NimmLor/7-Segement-Clock/images/arduino_code.PNG

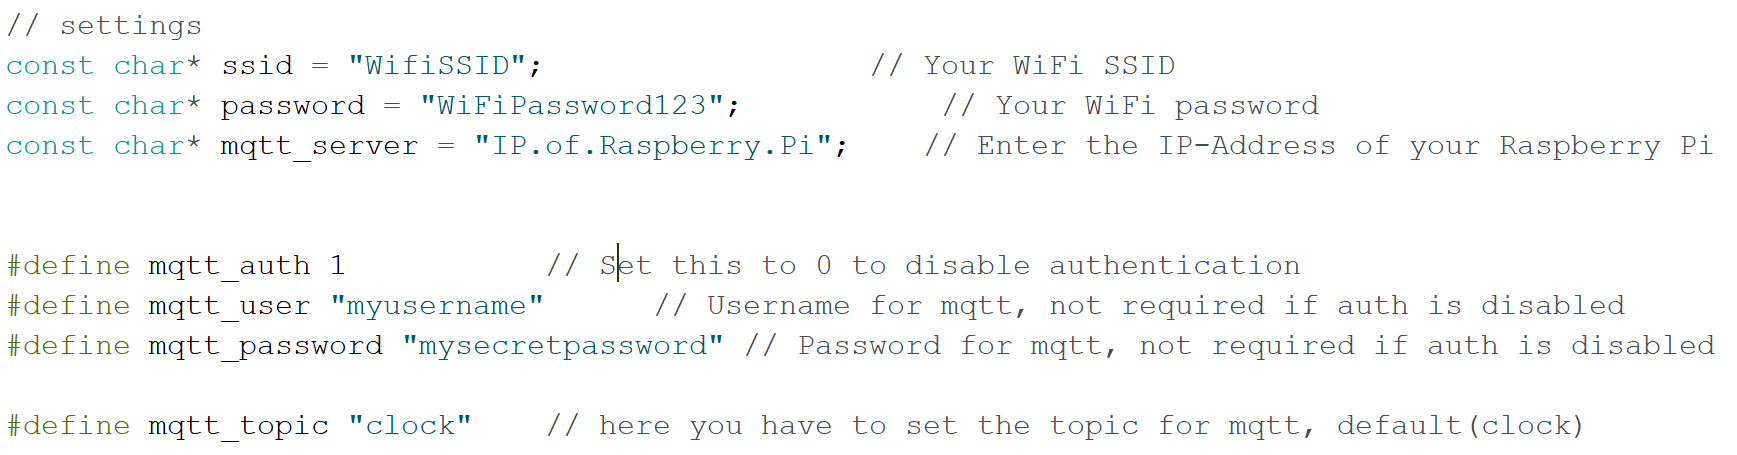
images/arduino_code.PNG
