NimmLor/7-Segement-Clock/images/customize_dashboards2.PNG

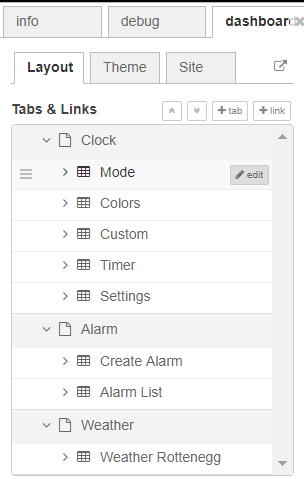
images/customize_dashboards2.PNG
