NimmLor/7-Segement-Clock/images/customize_webinterface.PNG

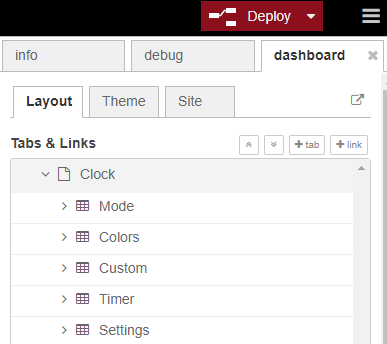
images/customize_webinterface.PNG
