NimmLor/7-Segement-Clock/images/DSC_1147.JPG

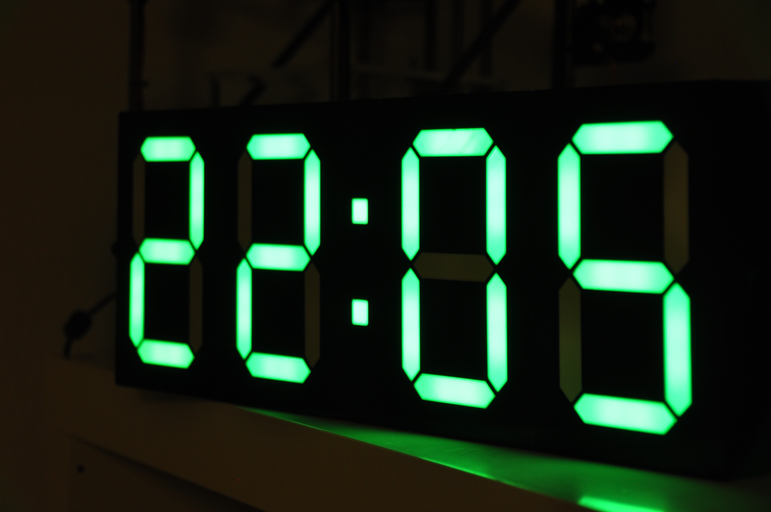
images/DSC_1147.JPG
