NimmLor/7-Segement-Clock/images/DSC_1149.JPG

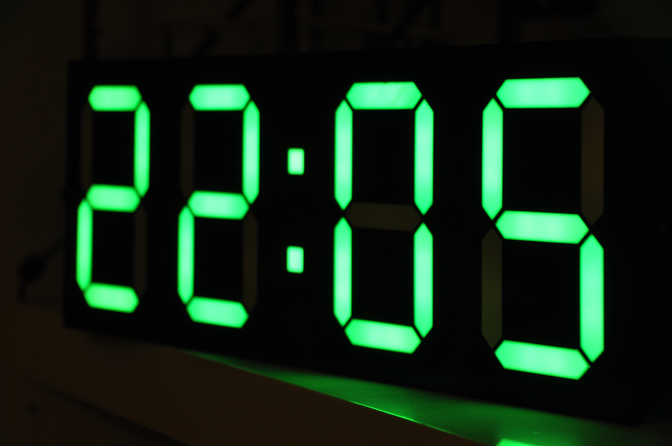
images/DSC_1149.JPG
