NimmLor/7-Segement-Clock/images/DSC_1150.JPG

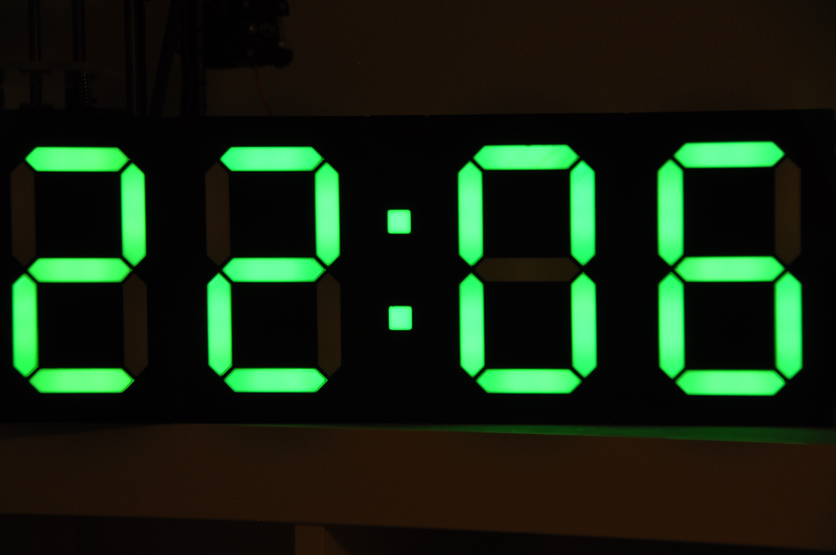
images/DSC_1150.JPG
