NimmLor/7-Segement-Clock/images/DSC_1151.JPG

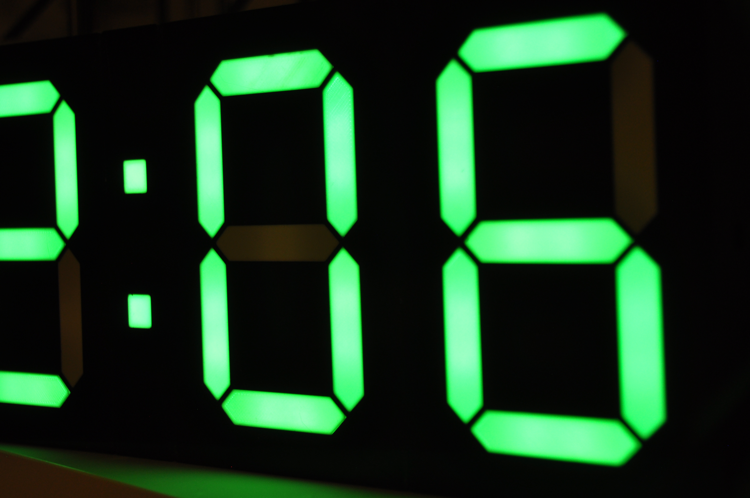
images/DSC_1151.JPG
