NimmLor/7-Segement-Clock/images/DSC_1152.JPG

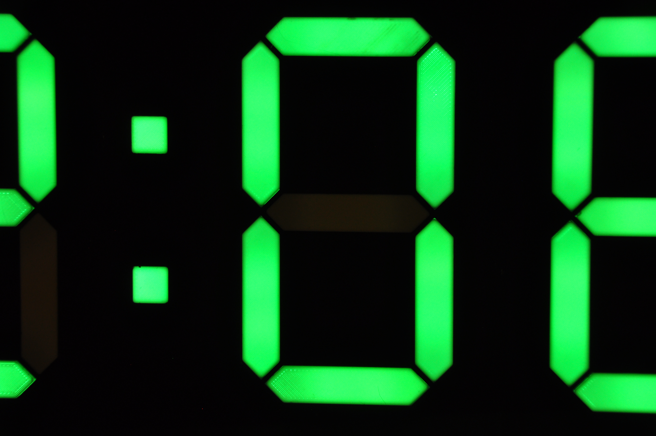
images/DSC_1152.JPG
