NimmLor/7-Segement-Clock/images/DSC_1153.JPG

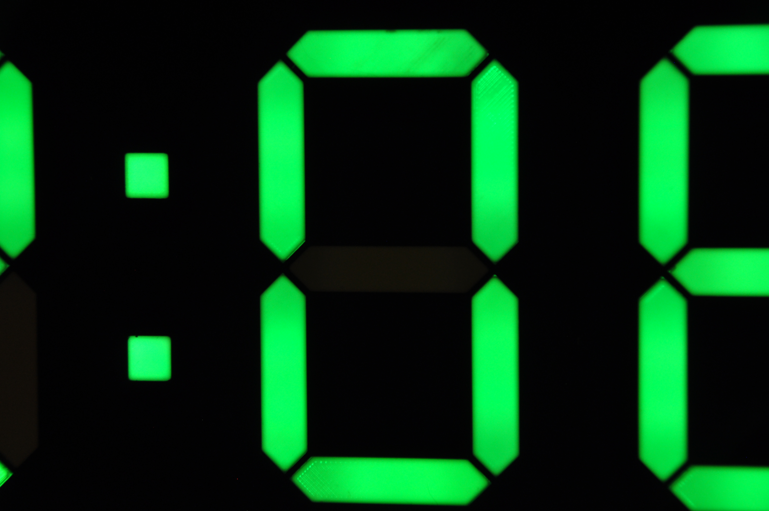
images/DSC_1153.JPG
