NimmLor/7-Segement-Clock/images/DSC_1157.JPG

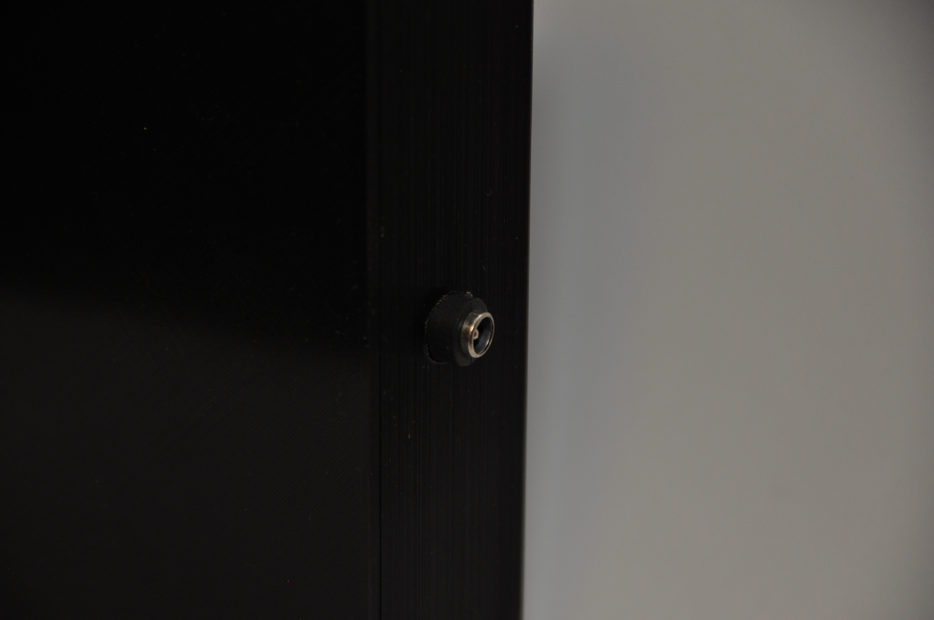
images/DSC_1157.JPG
