NimmLor/7-Segement-Clock/images/DSC_1158.JPG

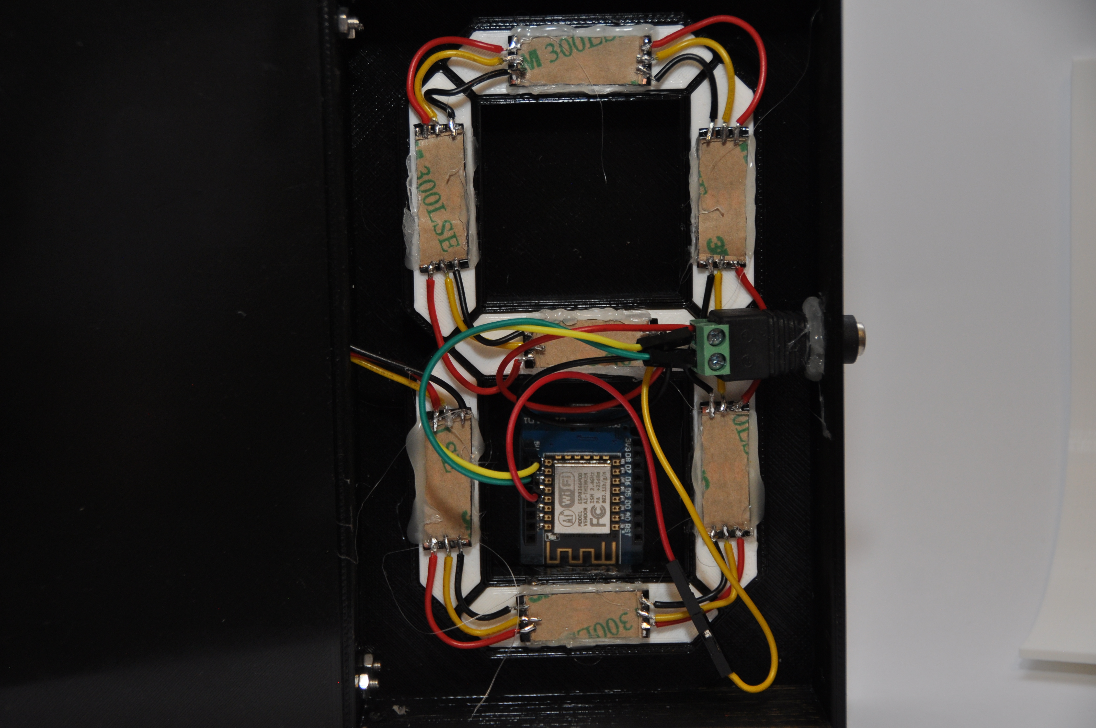
images/DSC_1158.JPG
