NimmLor/7-Segement-Clock/images/DSC_1159.JPG

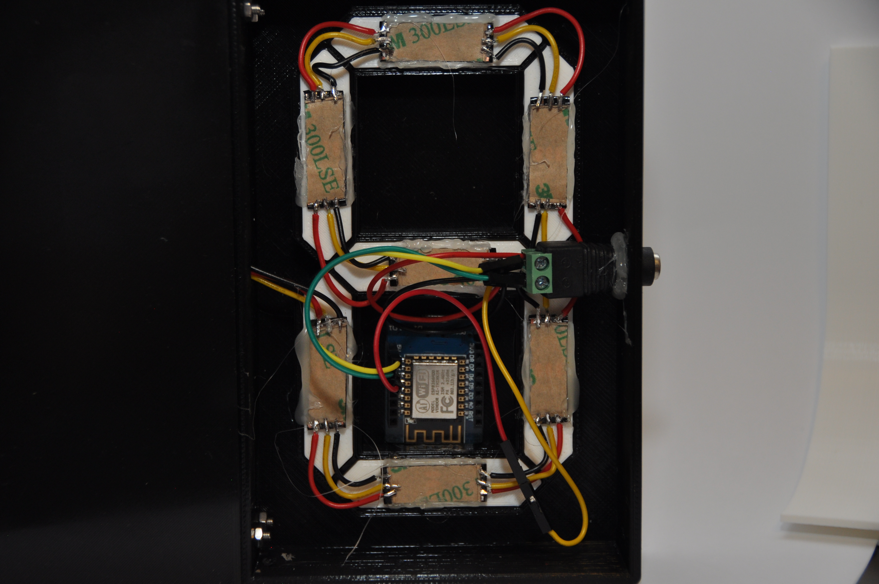
images/DSC_1159.JPG
