NimmLor/7-Segement-Clock/images/DSC_1160.JPG

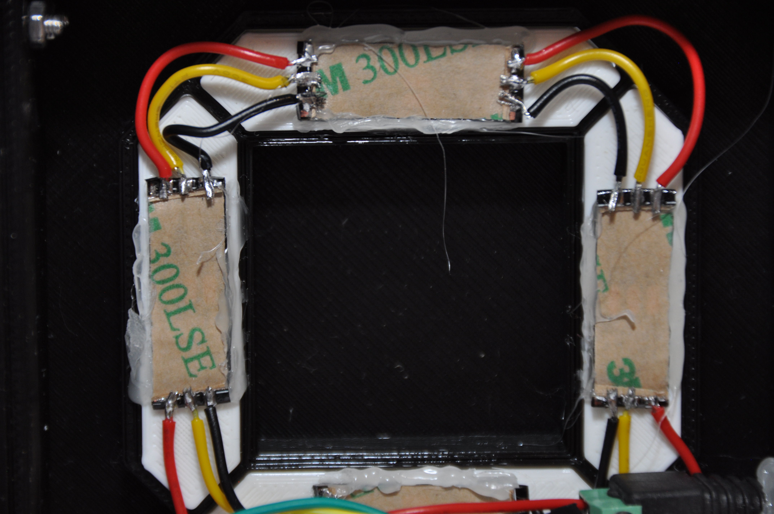
images/DSC_1160.JPG
