NimmLor/7-Segement-Clock/images/DSC_1161.JPG

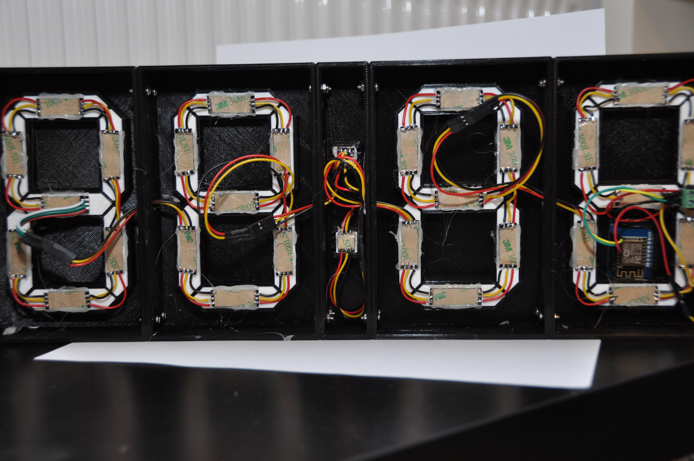
images/DSC_1161.JPG
