NimmLor/7-Segement-Clock/images/DSC_1162.JPG

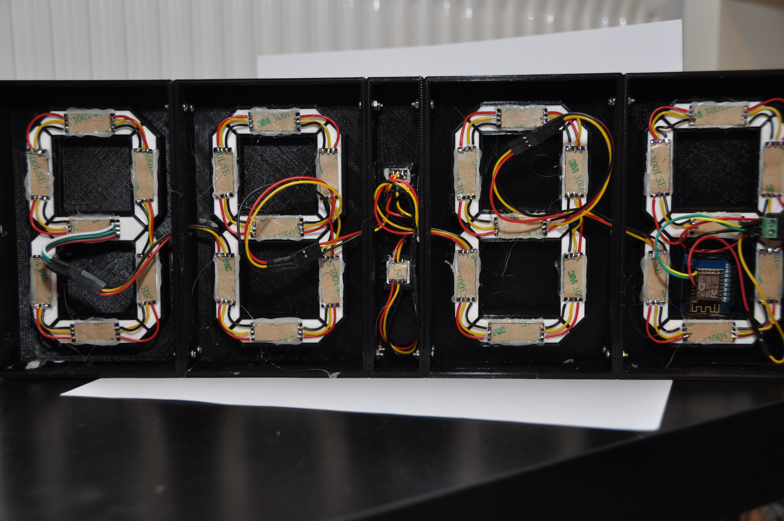
images/DSC_1162.JPG
