NimmLor/7-Segement-Clock/images/DSC_1163.JPG

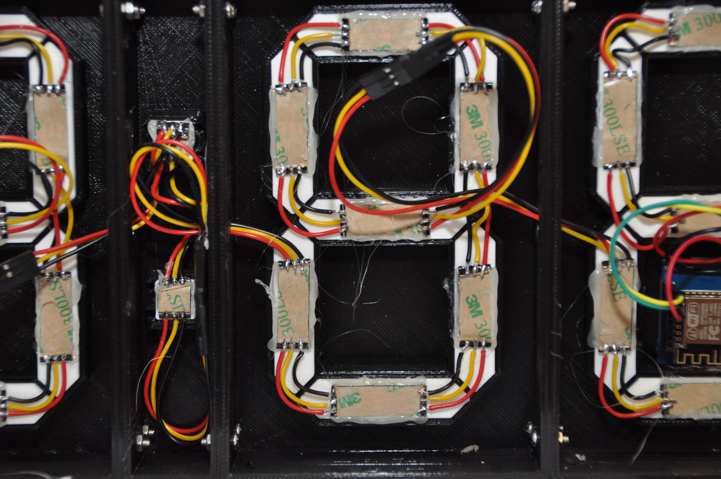
images/DSC_1163.JPG
