NimmLor/7-Segement-Clock/images/DSC_1164.JPG

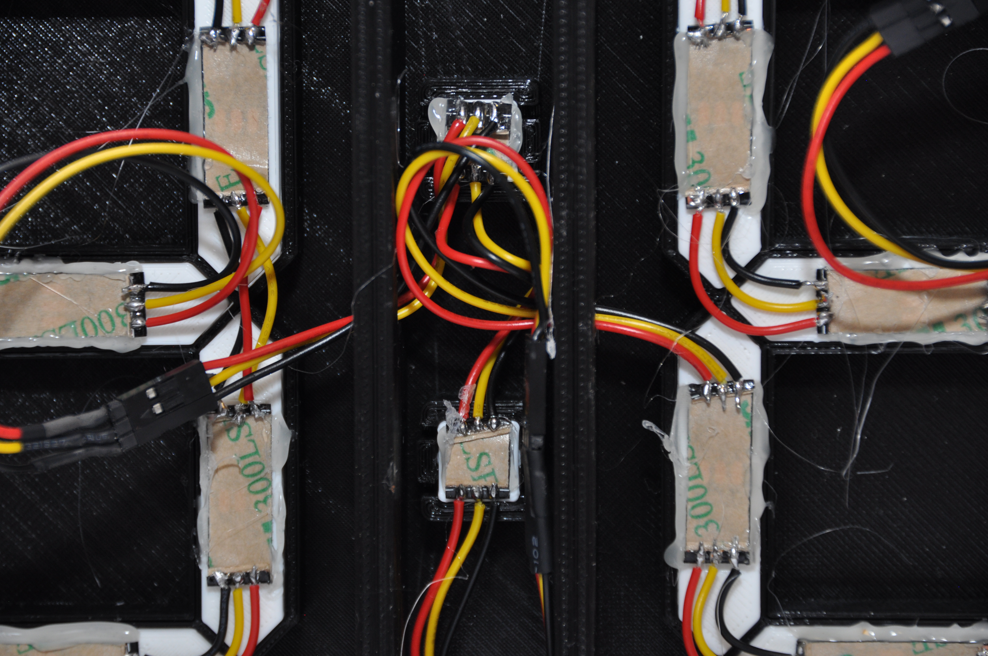
images/DSC_1164.JPG
