NimmLor/7-Segement-Clock/images/DSC_1166.JPG

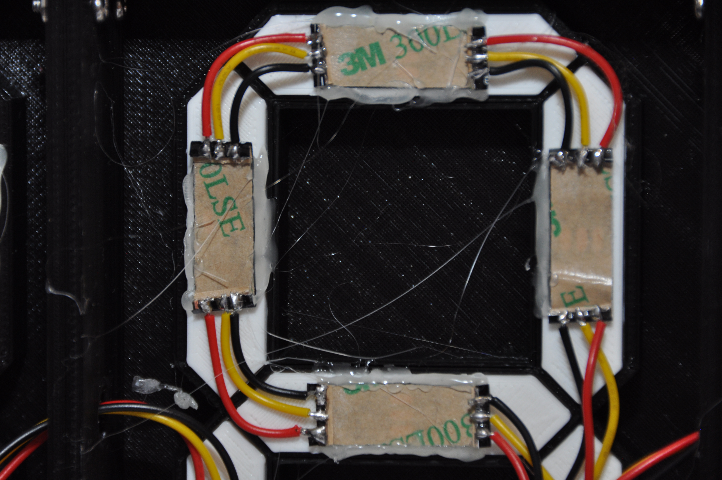
images/DSC_1166.JPG
