NimmLor/7-Segement-Clock/images/DSC_1168.JPG

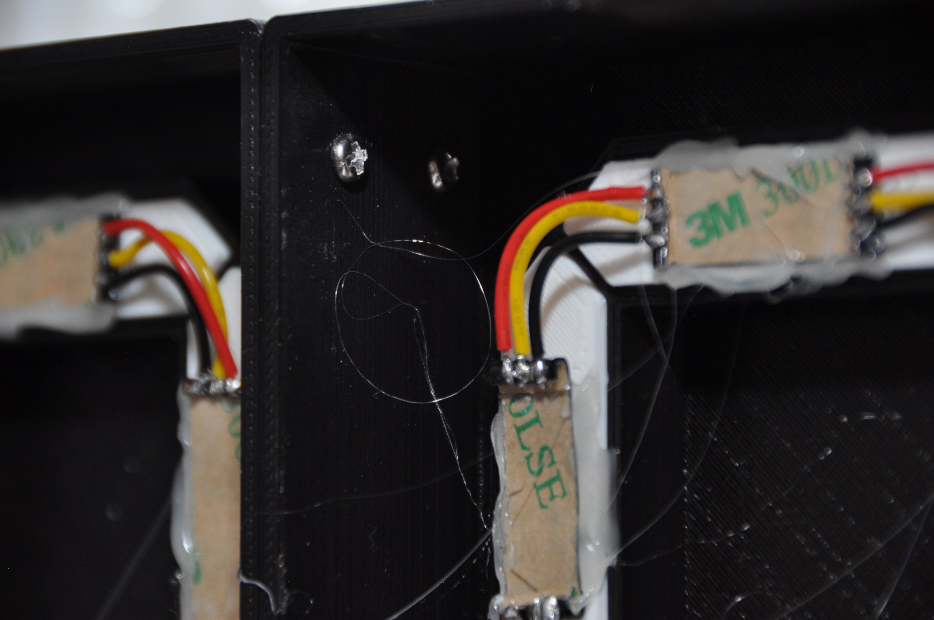
images/DSC_1168.JPG
