NimmLor/7-Segement-Clock/images/DSC_1169.JPG

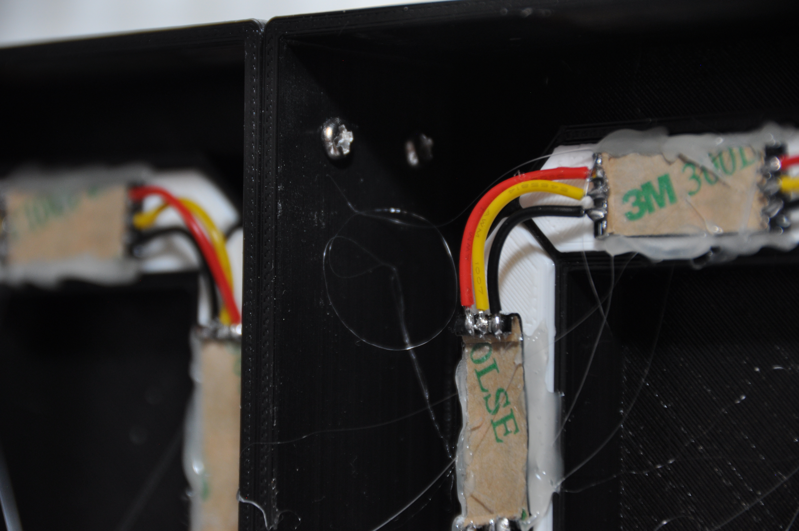
images/DSC_1169.JPG
