NimmLor/7-Segement-Clock/images/DSC_1170.JPG

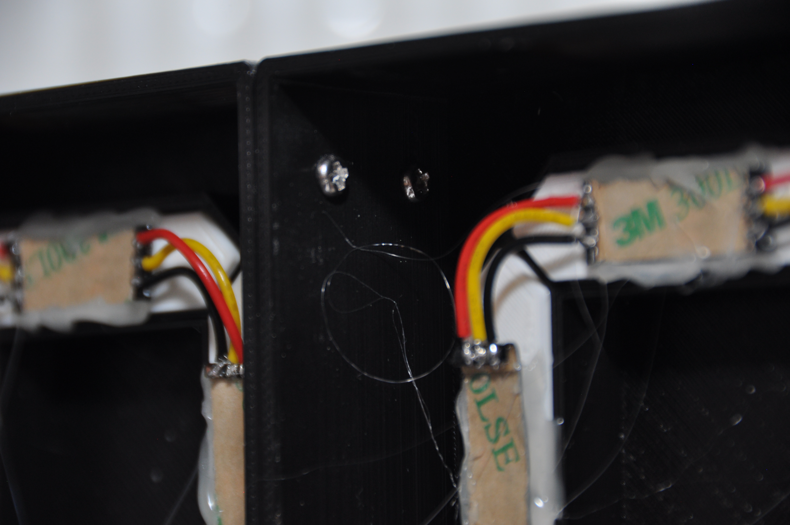
images/DSC_1170.JPG
