NimmLor/7-Segement-Clock/images/DSC_1171.JPG

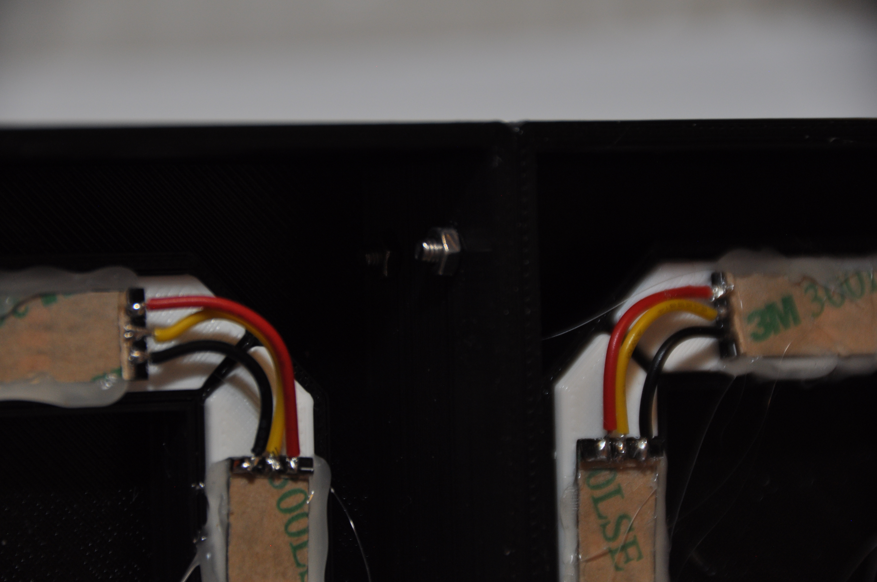
images/DSC_1171.JPG
