NimmLor/7-Segement-Clock/images/DSC_1172.JPG

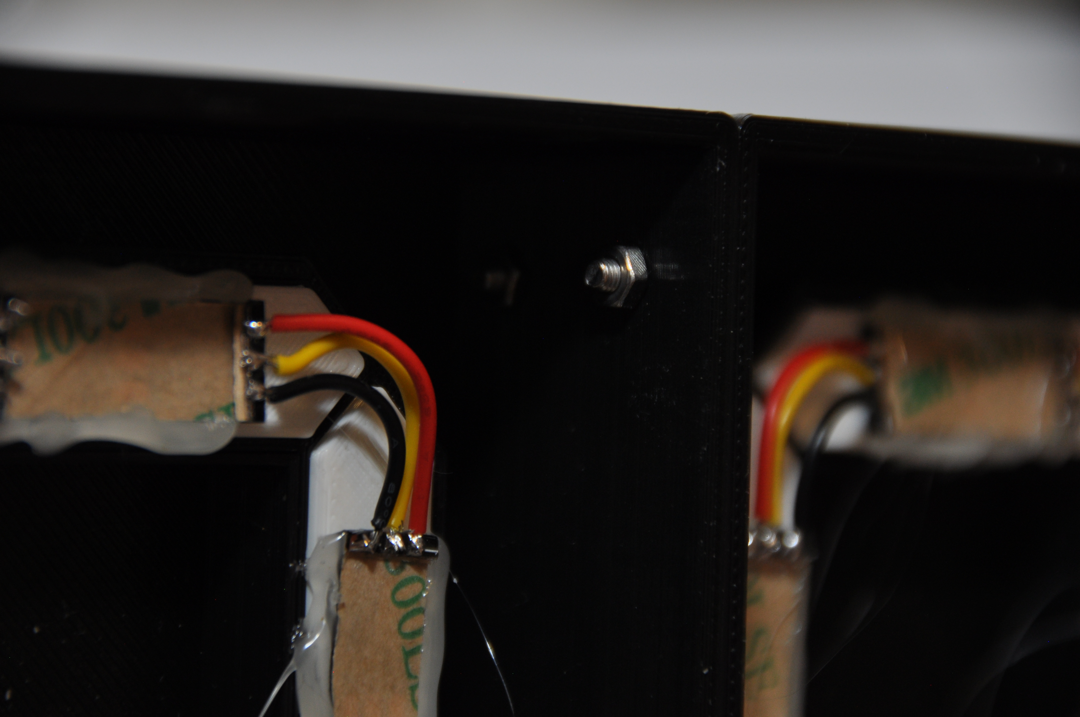
images/DSC_1172.JPG
