NimmLor/7-Segement-Clock/images/DSC_1175.JPG

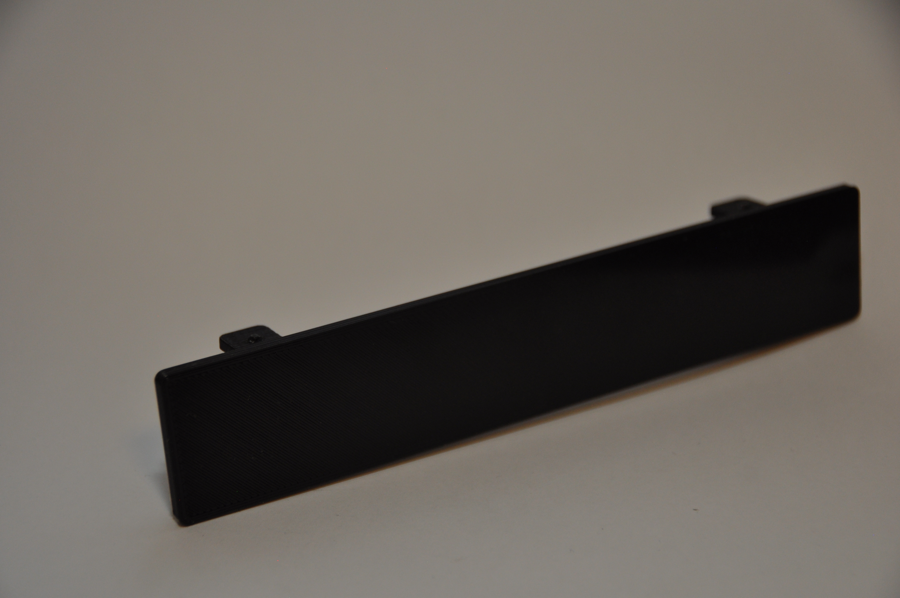
images/DSC_1175.JPG
