NimmLor/7-Segement-Clock/images/DSC_1179.JPG

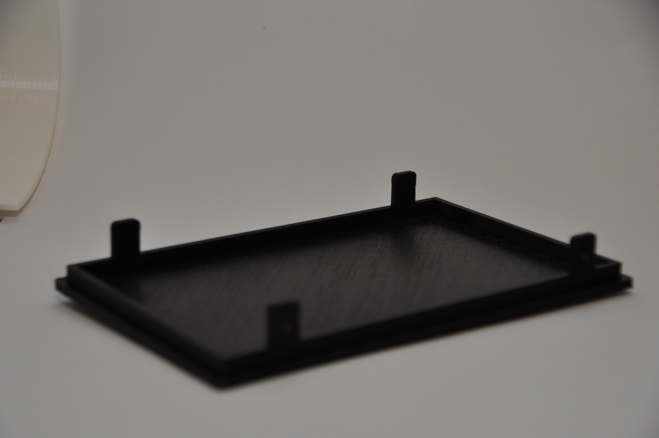
images/DSC_1179.JPG
