NimmLor/7-Segement-Clock/images/DSC_1180.JPG

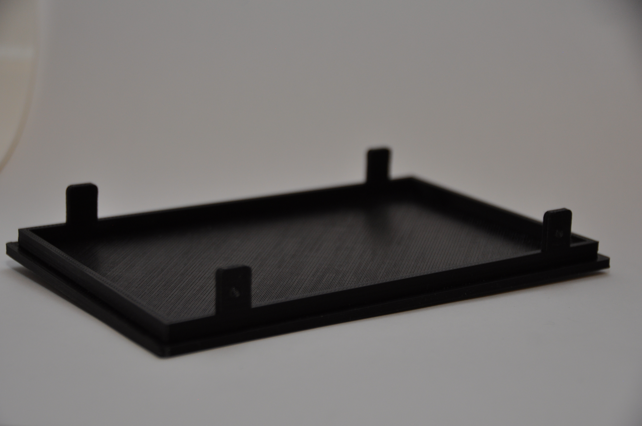
images/DSC_1180.JPG
