NimmLor/7-Segement-Clock/images/DSC_1181.JPG

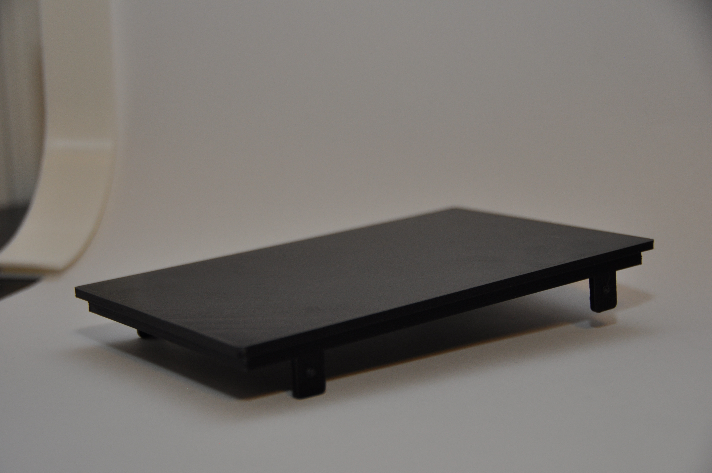
images/DSC_1181.JPG
