NimmLor/7-Segement-Clock/images/DSC_1182.JPG

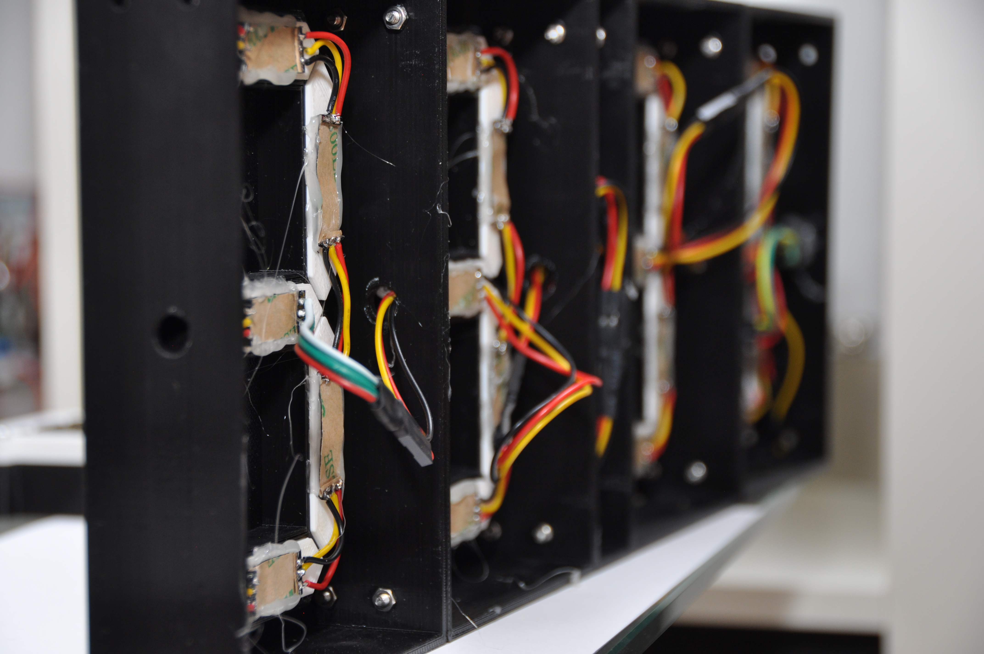
images/DSC_1182.JPG
