NimmLor/7-Segement-Clock/images/DSC_1184.JPG

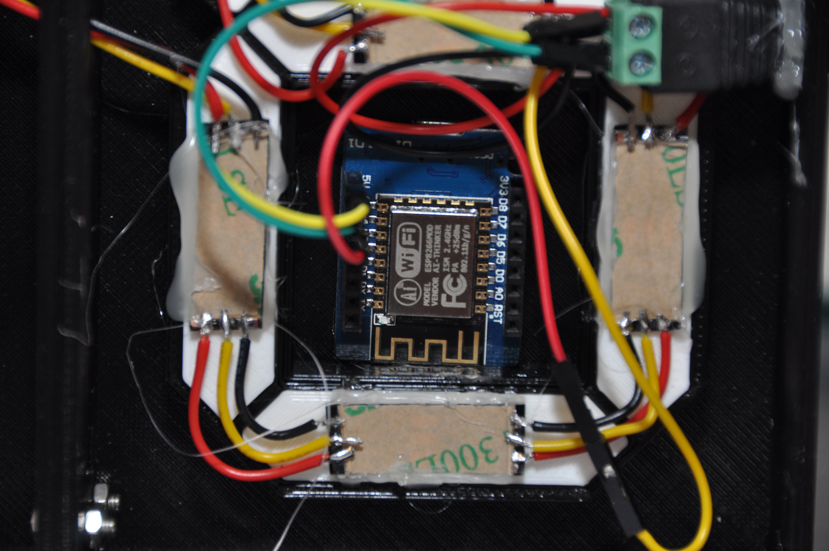
images/DSC_1184.JPG
