NimmLor/7-Segement-Clock/images/DSC_1185.JPG

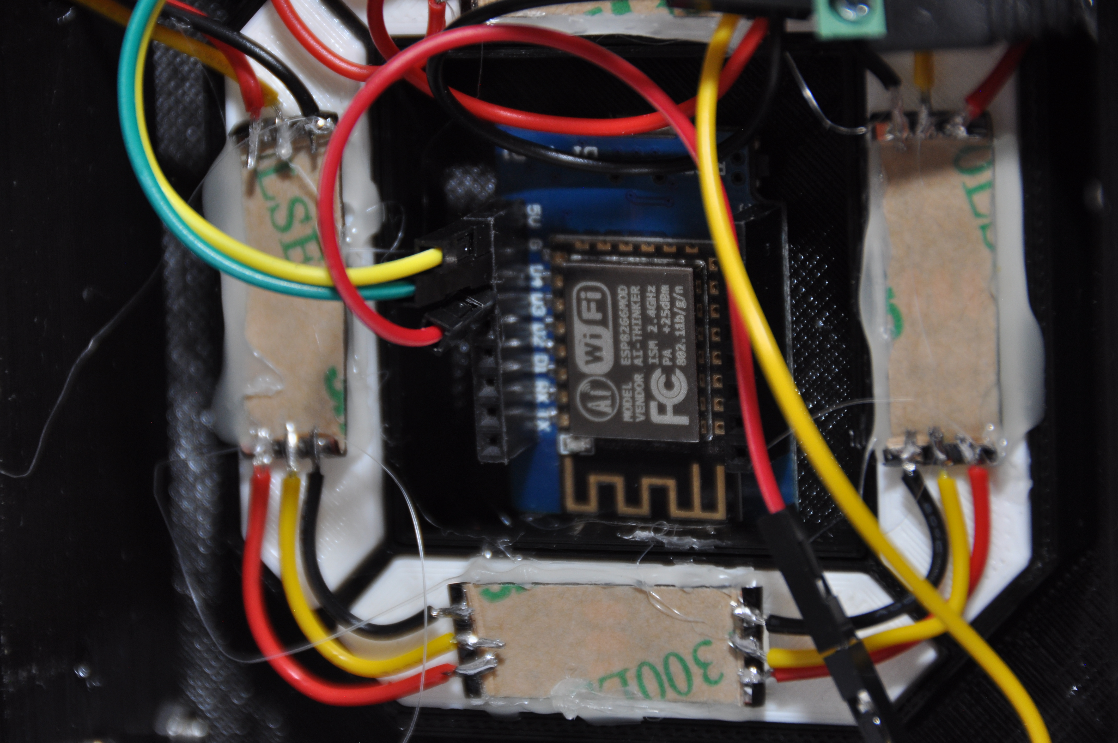
images/DSC_1185.JPG
