NimmLor/7-Segement-Clock/images/DSC_1186.JPG

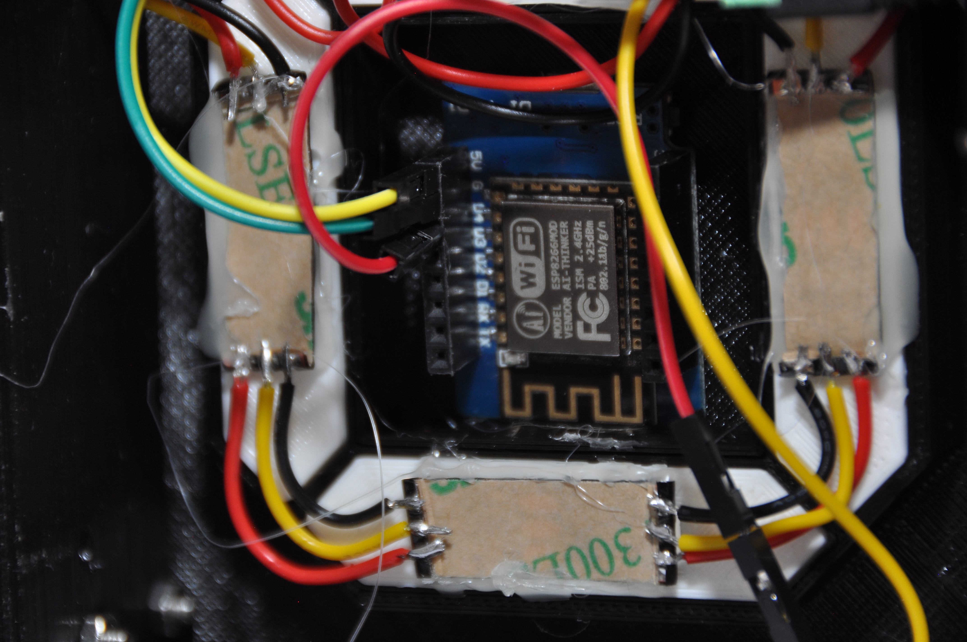
images/DSC_1186.JPG
