NimmLor/7-Segement-Clock/images/edit_width1.PNG

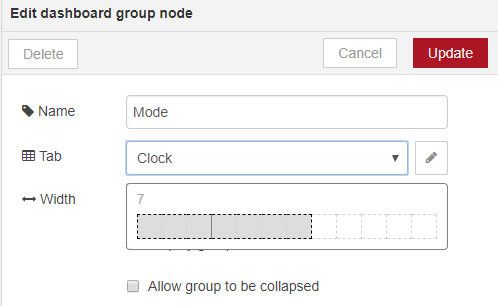
images/edit_width1.PNG
