NimmLor/7-Segement-Clock/images/edit_width2.PNG

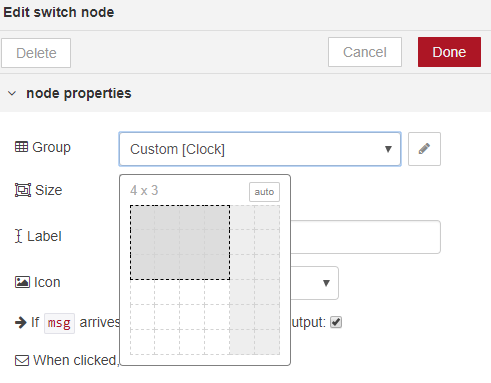
images/edit_width2.PNG
