NimmLor/7-Segement-Clock/images/IMG_20180430_115424.jpg

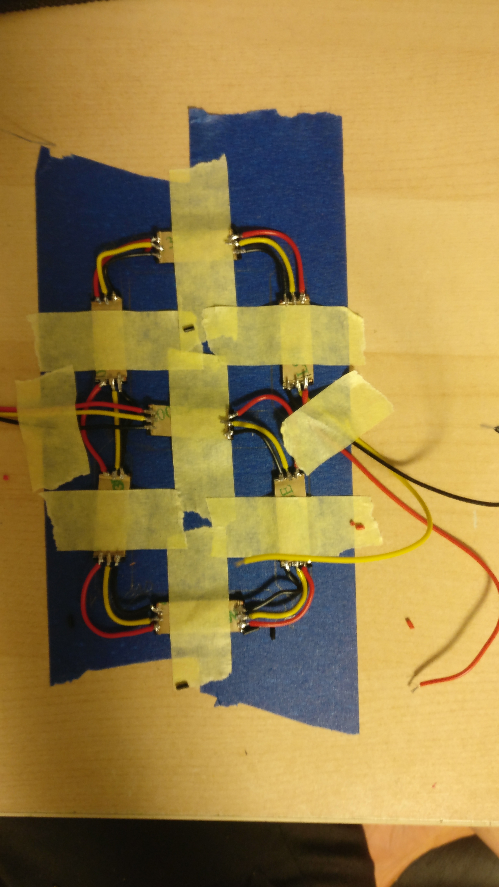
images/IMG_20180430_115424.jpg
