NimmLor/7-Segement-Clock/images/IMG_20180430_164632.jpg

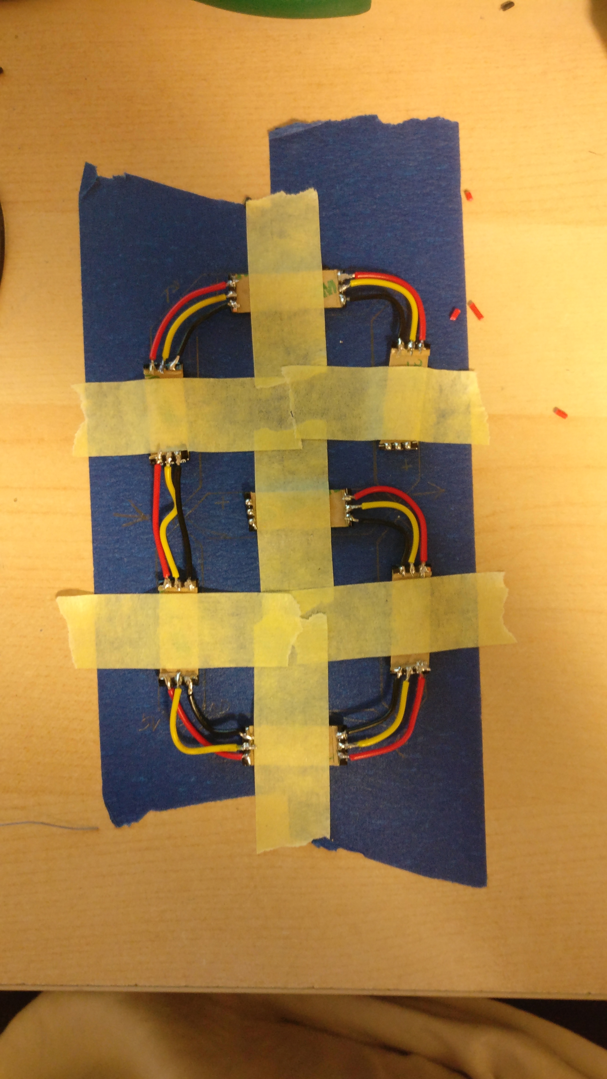
images/IMG_20180430_164632.jpg
