NimmLor/7-Segement-Clock/images/IMG_20180505_133125.jpg

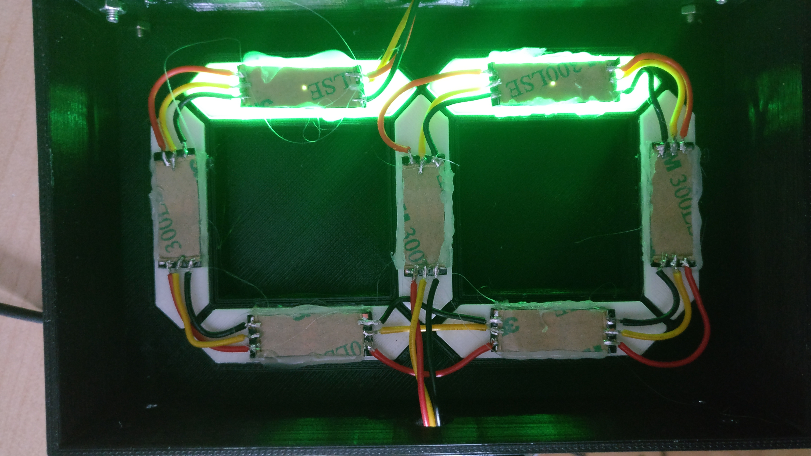
images/IMG_20180505_133125.jpg
