NimmLor/7-Segement-Clock/images/IMG_20180616_221109.jpg

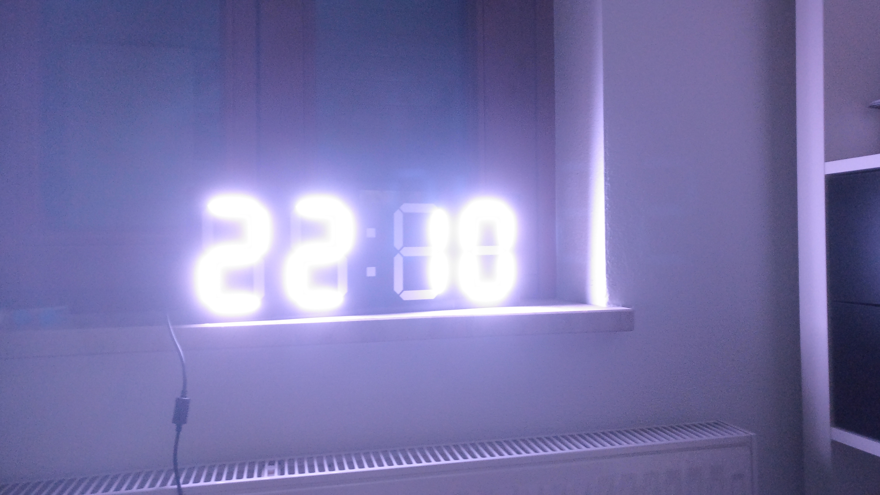
images/IMG_20180616_221109.jpg
