NimmLor/7-Segement-Clock/images/IMG_20180616_221110 1.jpg

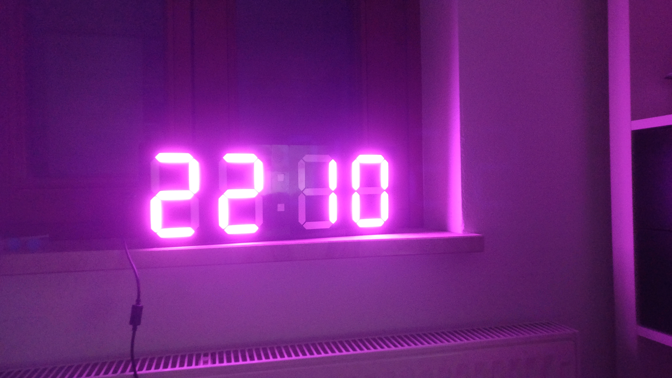
images/IMG_20180616_221110 1.jpg
