NimmLor/7-Segement-Clock/images/new/Screenshot_2018-09-24-22-27-50.png

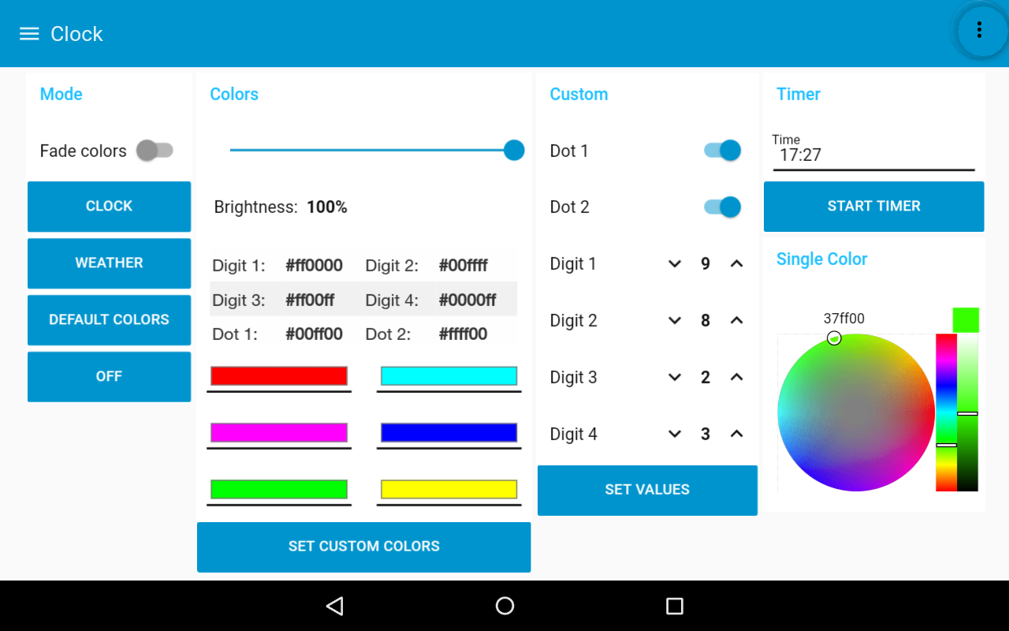
images/new/Screenshot_2018-09-24-22-27-50.png
