NimmLor/7-Segement-Clock/images/Screenshot_2018-06-16-22-03-41.png

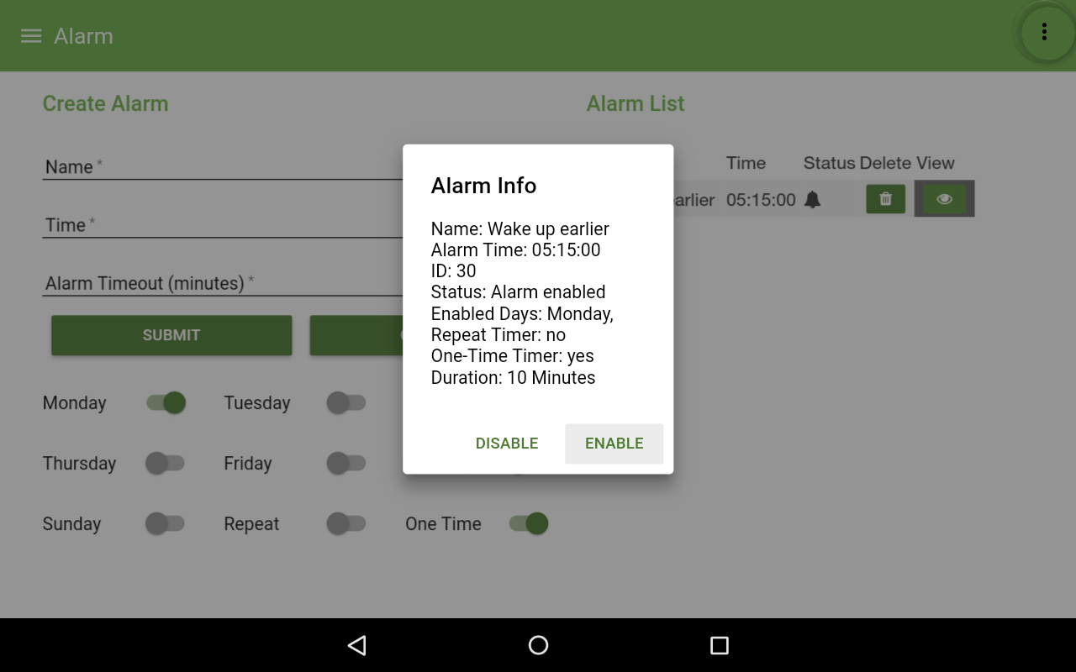
images/Screenshot_2018-06-16-22-03-41.png
