NimmLor/7-Segement-Clock/images/Screenshot_2018-06-16-22-17-32.png

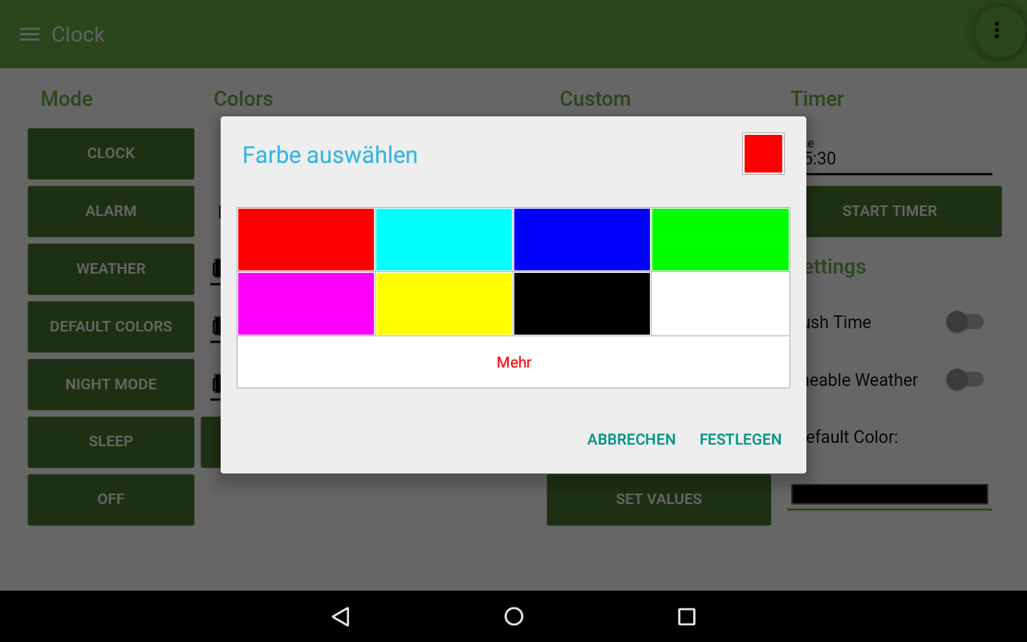
images/Screenshot_2018-06-16-22-17-32.png
