NimmLor/7-Segement-Clock/miniclock/gallary/usb_flasher.PNG

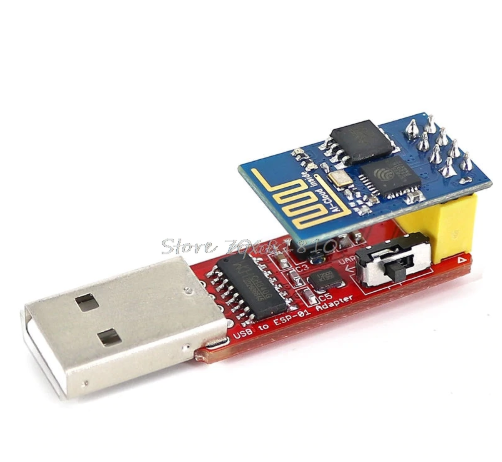
miniclock/gallary/usb_flasher.PNG
